EthanDP/mini-arcade/how-to-files/arduino_isp.png

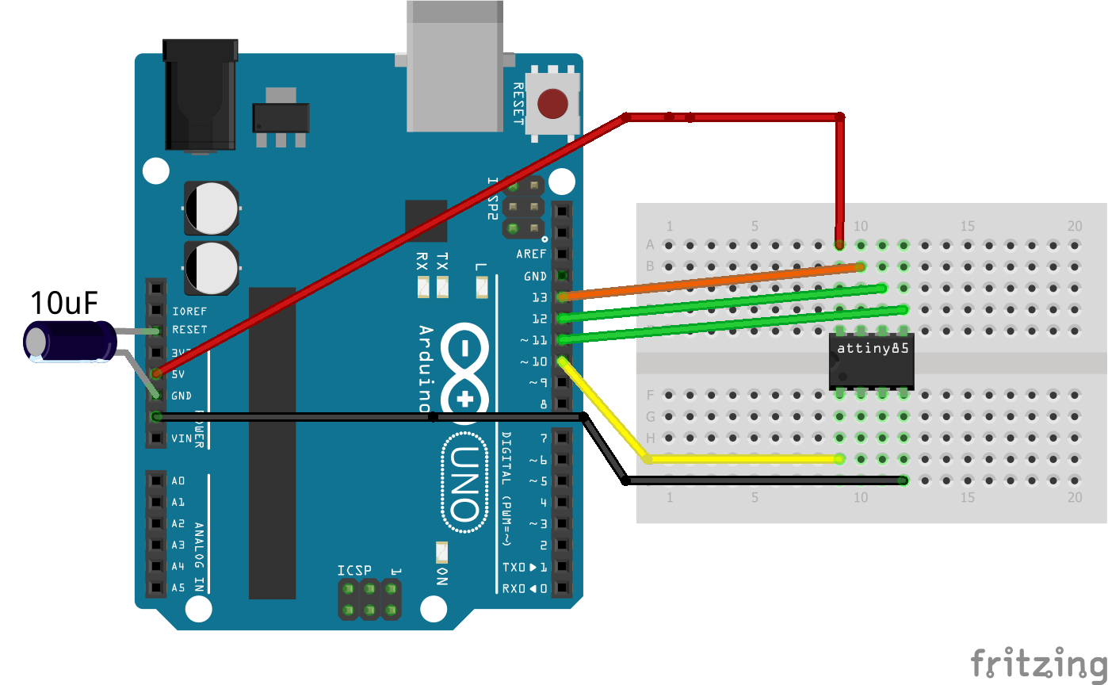
how-to-files/arduino_isp.png
