EthanDP/mini-arcade/how-to-files/button_board.png

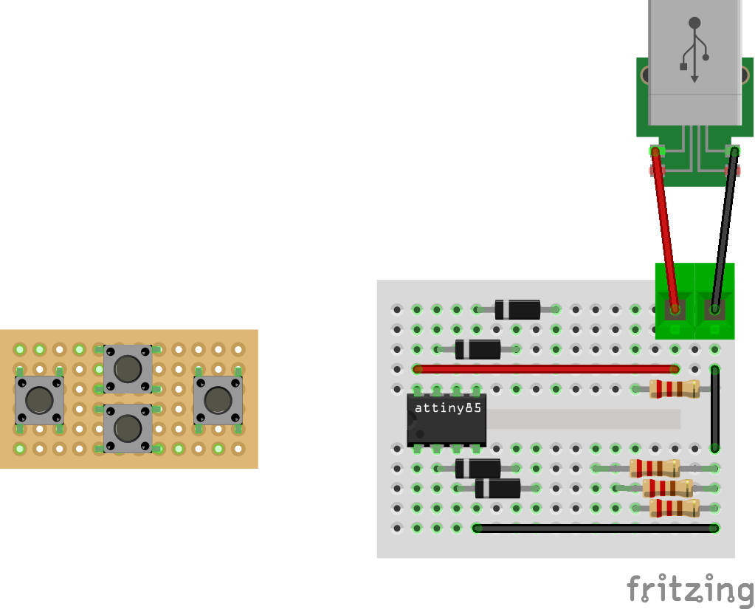
how-to-files/button_board.png
