EthanDP/mini-arcade/how-to-files/diode_placement.png

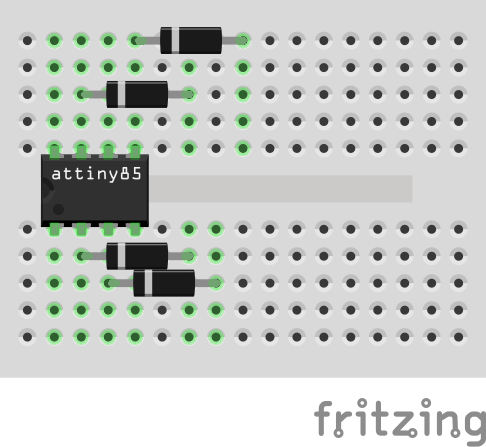
how-to-files/diode_placement.png
