EthanDP/mini-arcade/src/simon/timings.h

#ifndef TIMING_HEADER
#define TIMING_HEADER

#ifndef CLOCK_SPEED
#define CLOCK_SPEED 1
#endif

#define PULSE 10
#define SHORT_1 80
#define SHORT_2 160
#define SHORT_3 280
#define MED_1 400
#define MED_2 600
#define LONG_1 800
#define LONG_2 1200

#endif
